Camilo-Mora/MorasPot/Images/IMG_3427.JPG

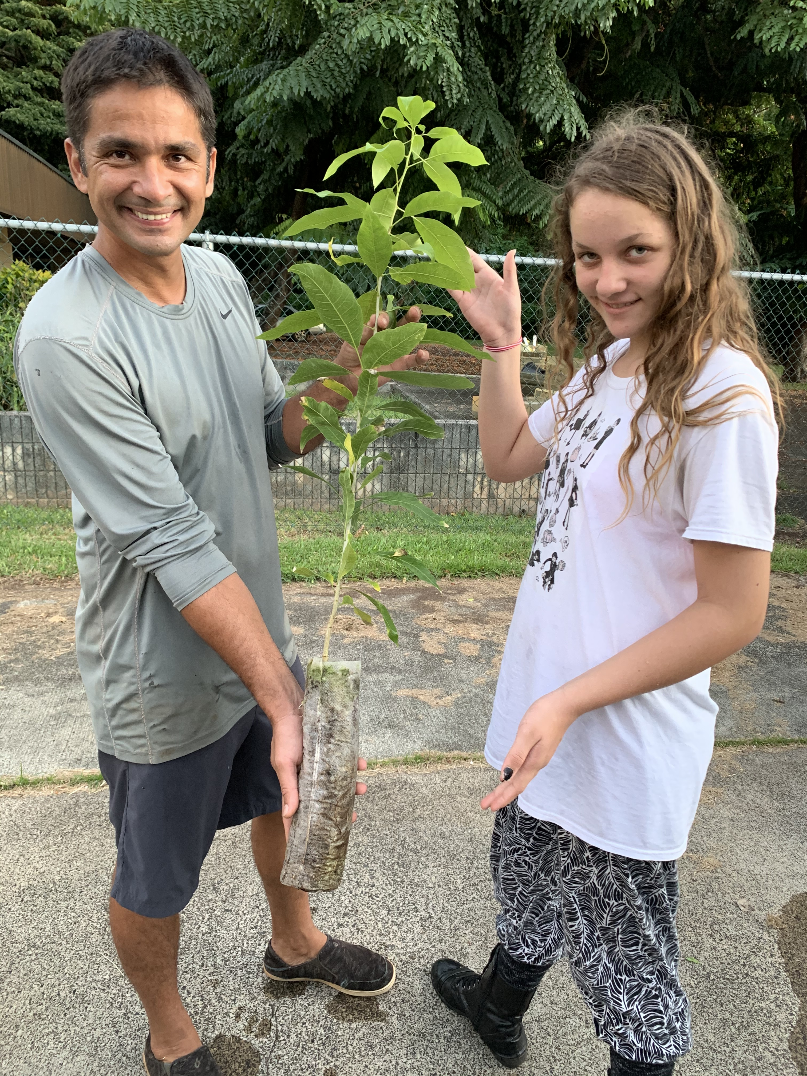
Images/IMG_3427.JPG
