Camilo-Mora/MorasPot/Images/IMG_3429.JPG

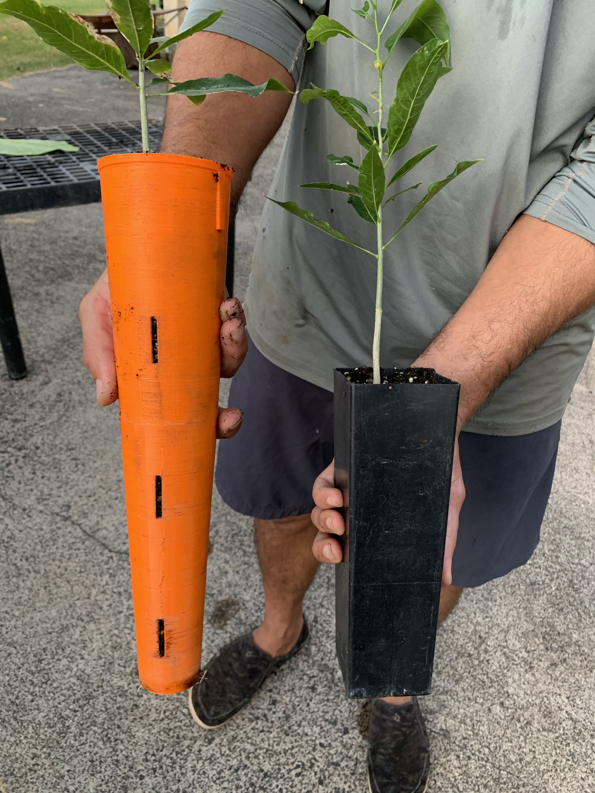
Images/IMG_3429.JPG
