Camilo-Mora/MorasPot/Images/IMG_3431.JPG

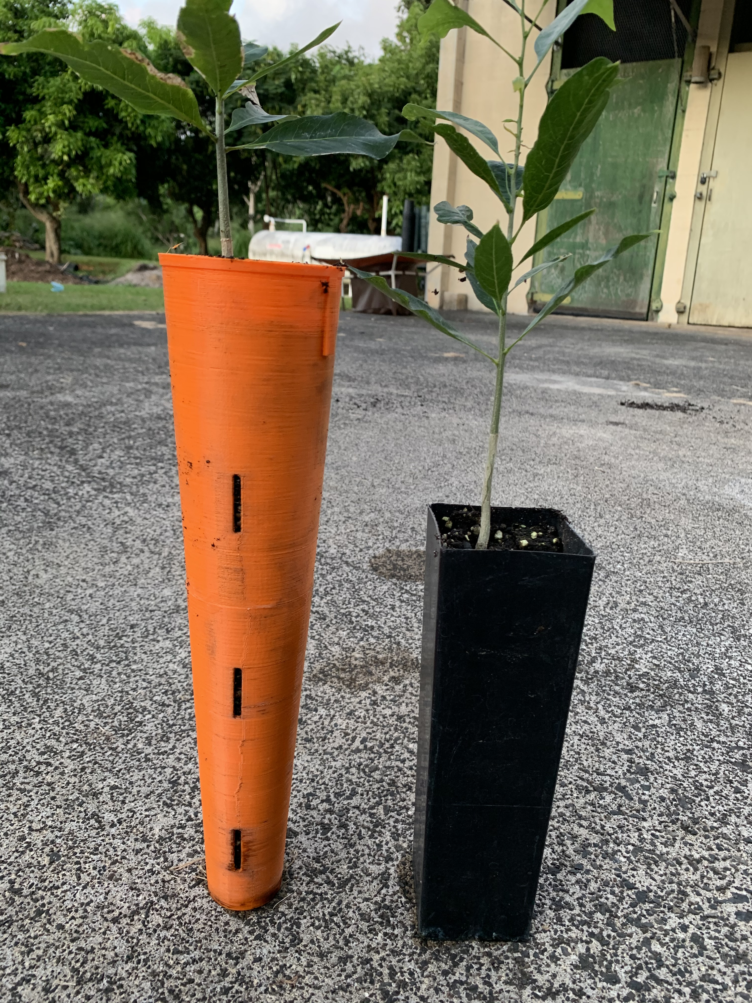
Images/IMG_3431.JPG
