Camilo-Mora/MorasPot/Images/IMG_7506.jpg

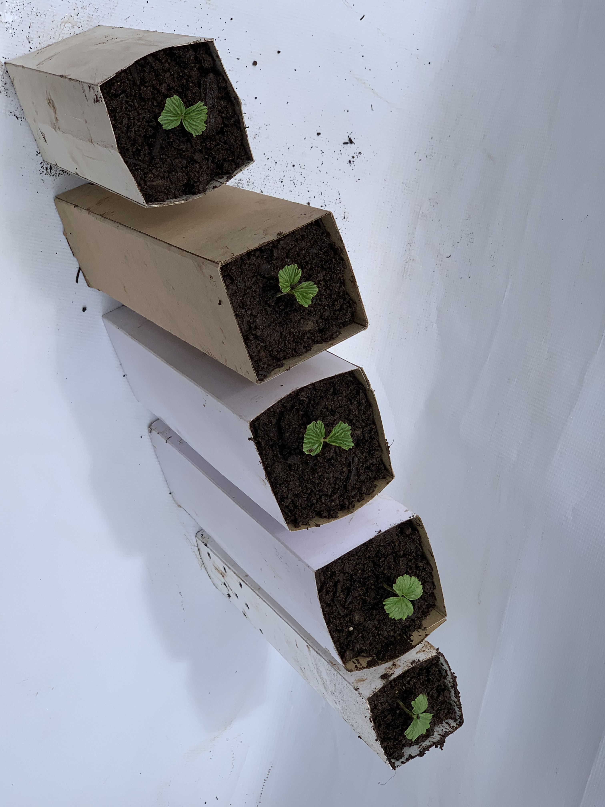
Images/IMG_7506.jpg
