Camilo-Mora/MorasPot/Images/IMG_7509.jpg

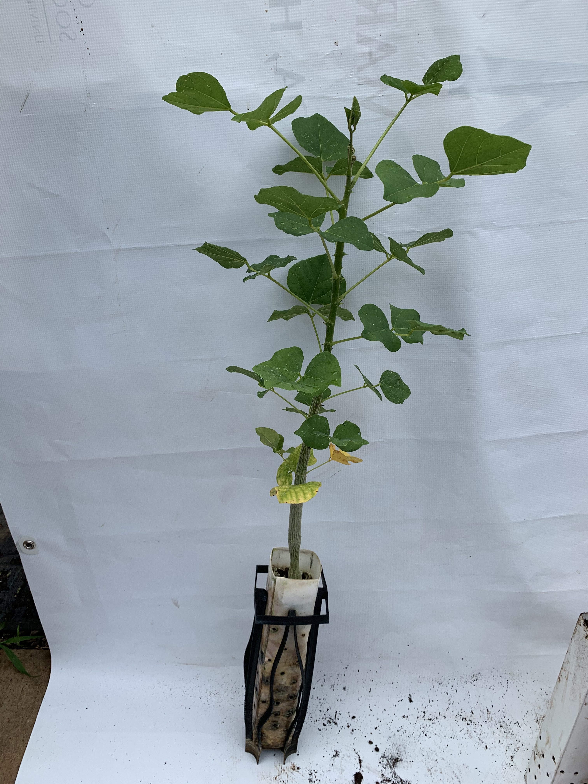
Images/IMG_7509.jpg
