Camilo-Mora/MorasPot/Images/Perched Water Table.png

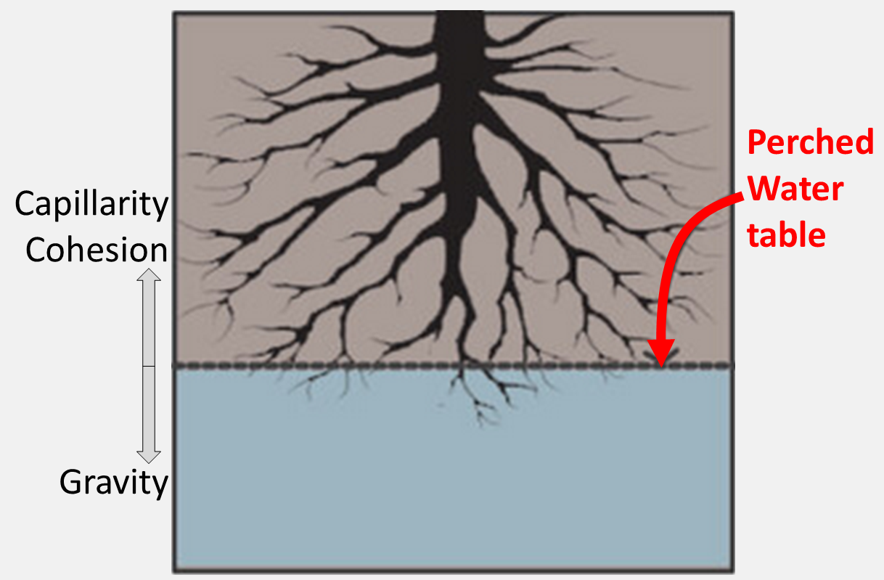
Images/Perched Water Table.png
