Camilo-Mora/MorasPot/Images/WIN_20210120_08_49_52_Pro.jpg

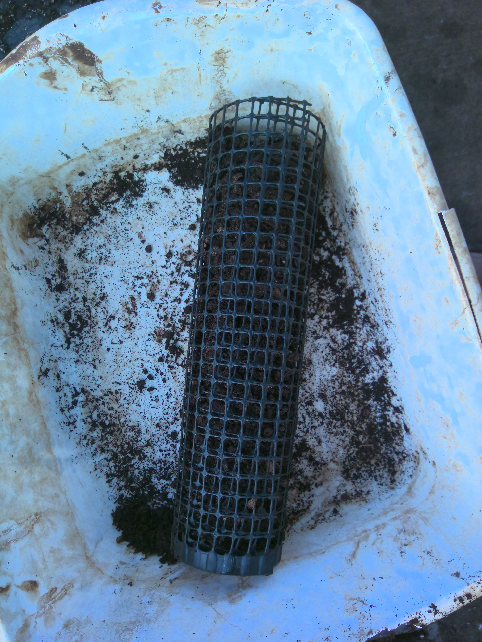
Images/WIN_20210120_08_49_52_Pro.jpg
