Camilo-Mora/MorasPot/Images/Fig.7.JPG

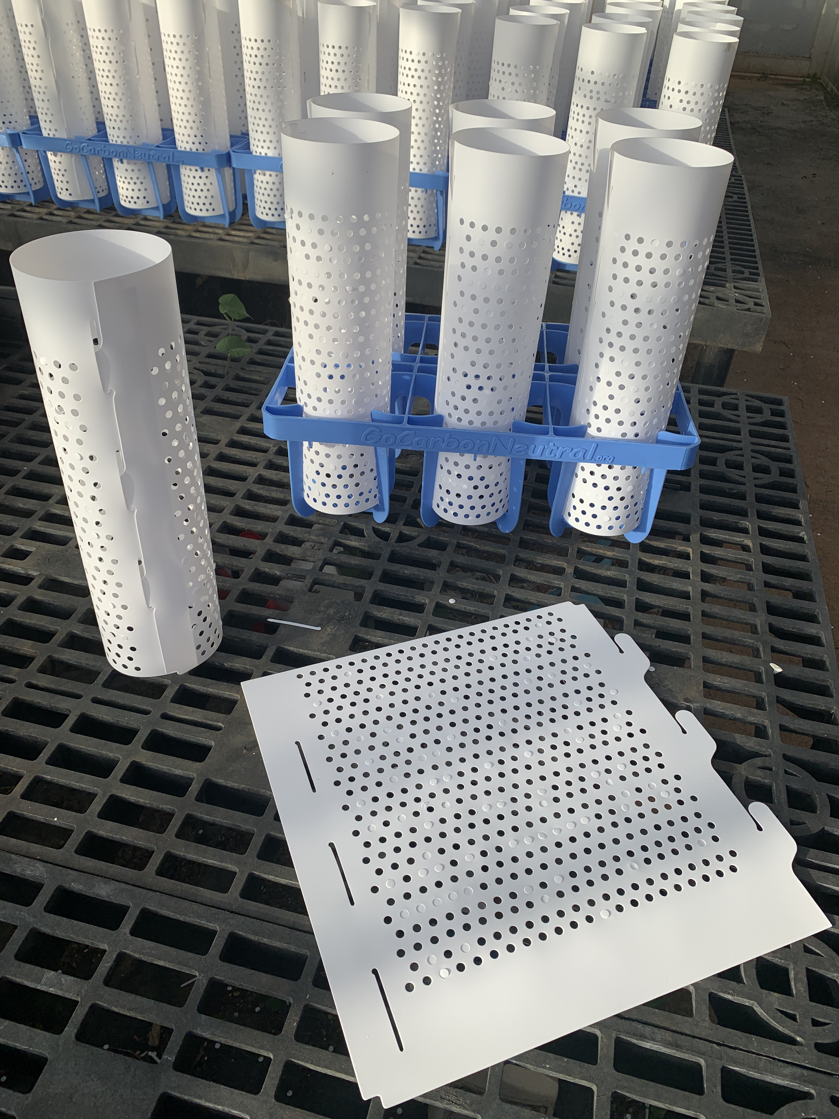
Images/Fig.7.JPG
