Camilo-Mora/MorasPot/Images/IMG_4424.jpg

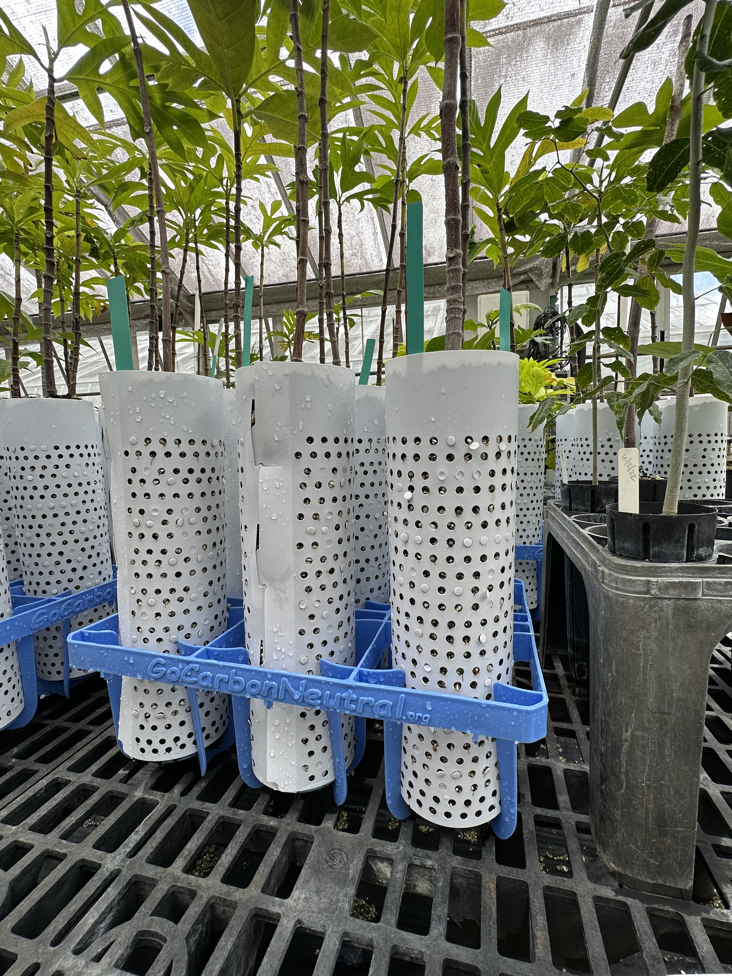
Images/IMG_4424.jpg
