Camilo-Mora/MorasPot/Images/IMG_4425.jpg

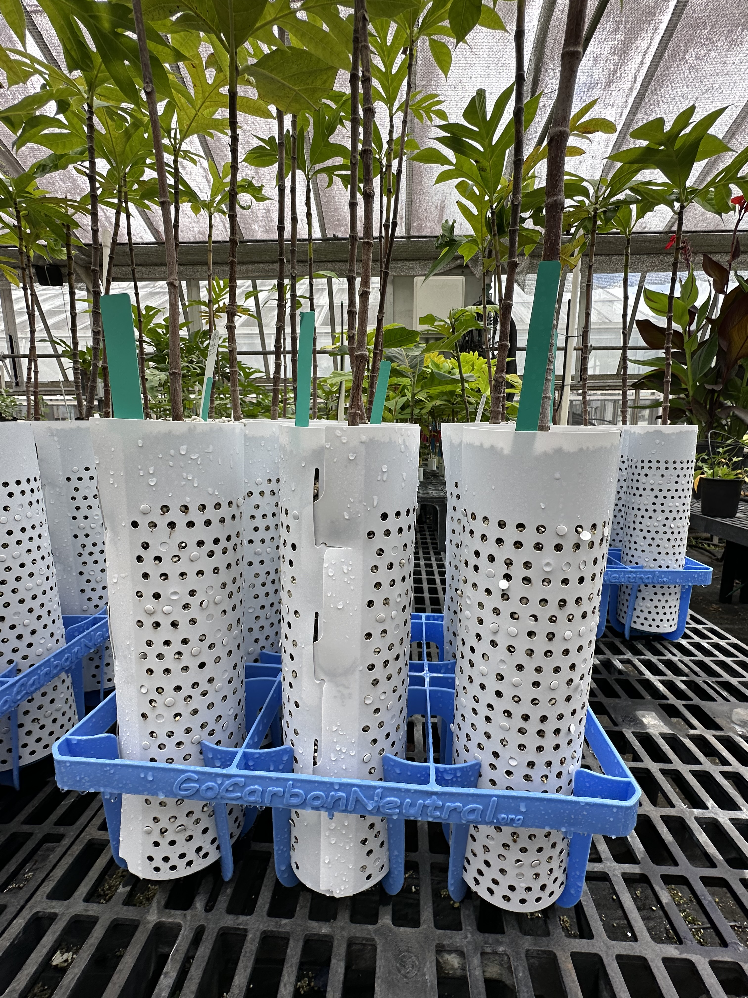
Images/IMG_4425.jpg
