Camilo-Mora/MorasPot/Images/IMG_4426.jpg

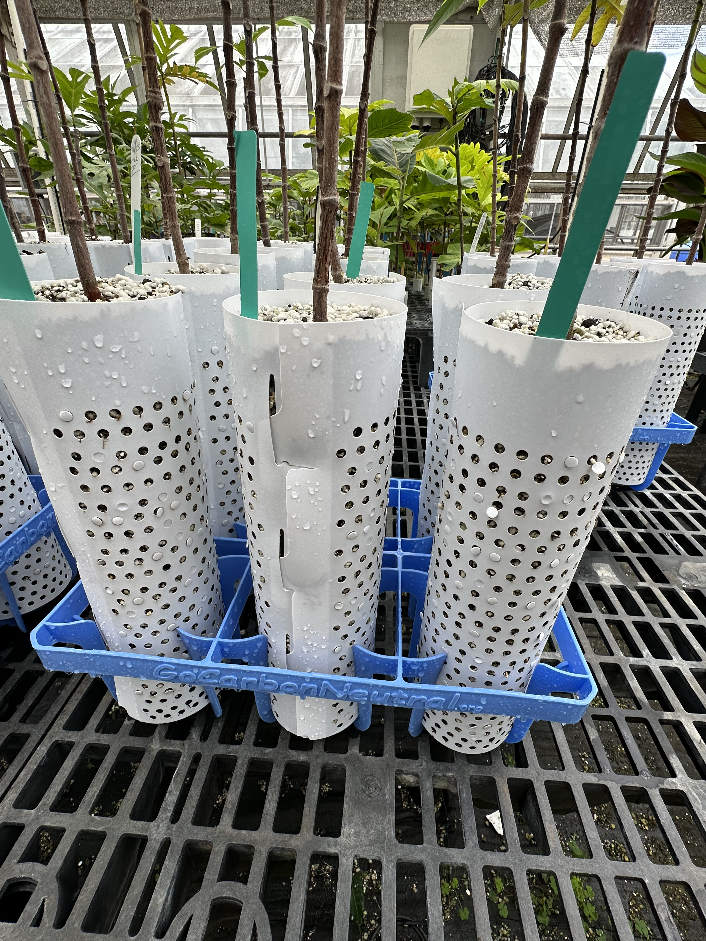
Images/IMG_4426.jpg
