Camilo-Mora/MorasPot/Images/IMG_7368.JPG

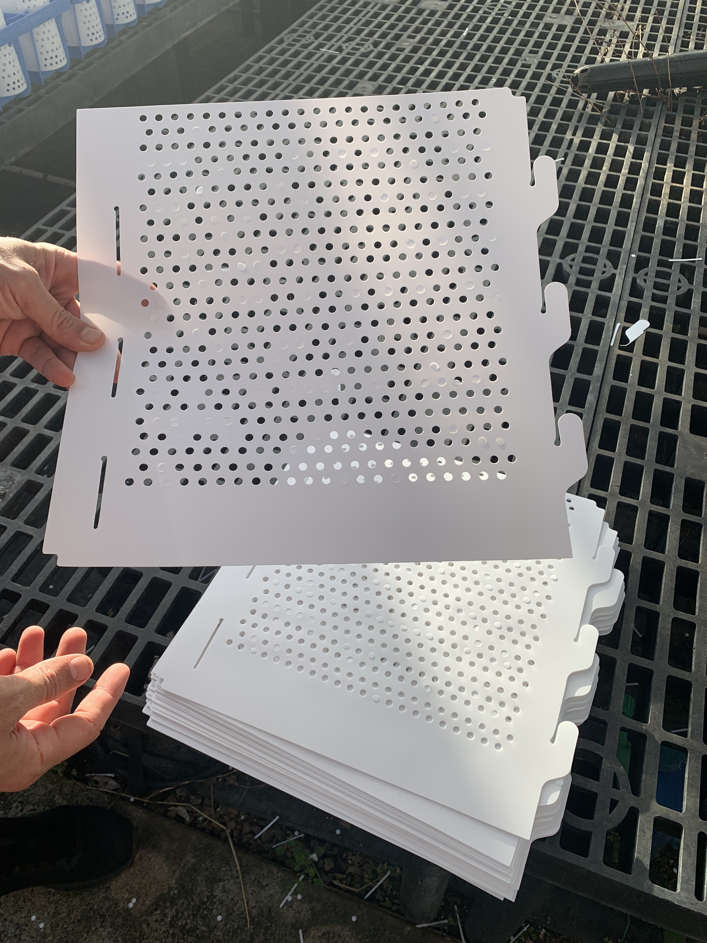
Images/IMG_7368.JPG
