Camilo-Mora/MorasPot/Images/RootBounding.jpg

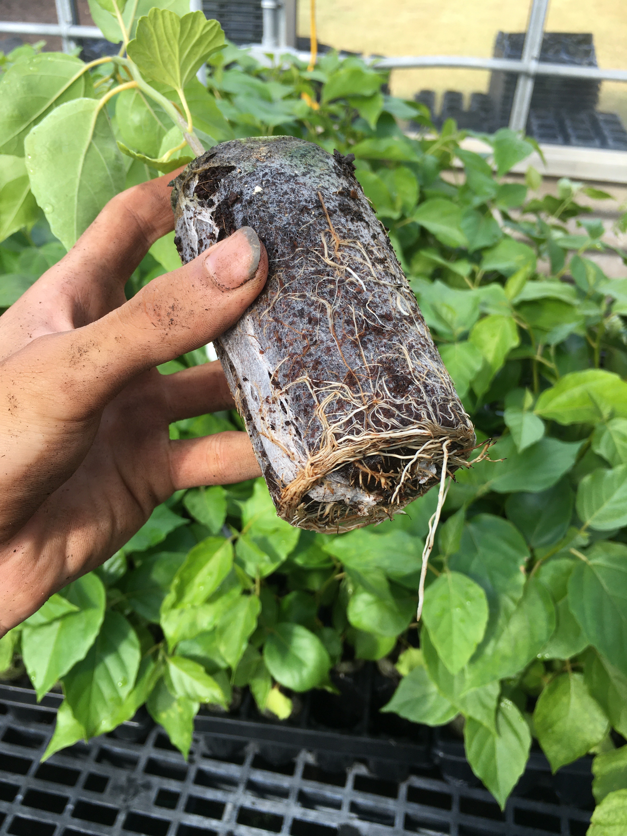
Images/RootBounding.jpg
